kekyo/ExtremeFeedbackDevice/images/v1/AssembleFinishing.jpg

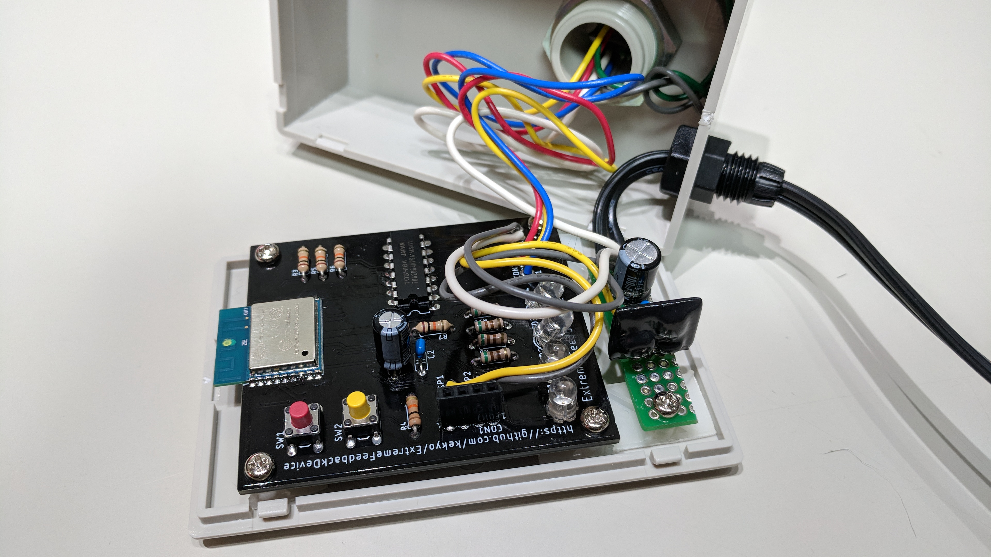
images/v1/AssembleFinishing.jpg
