kekyo/ExtremeFeedbackDevice/images/v1/AssembleUnit1.jpg

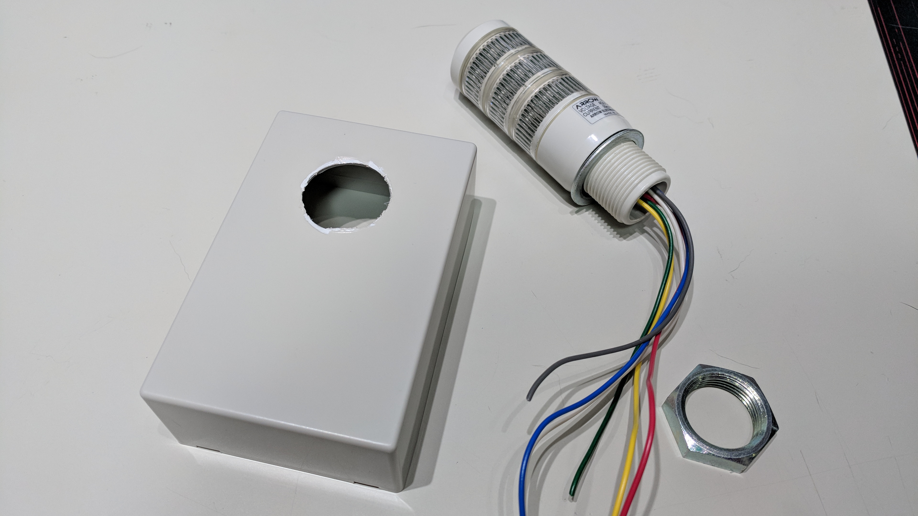
images/v1/AssembleUnit1.jpg
