kekyo/ExtremeFeedbackDevice/images/v1/AssembleUnit2.jpg

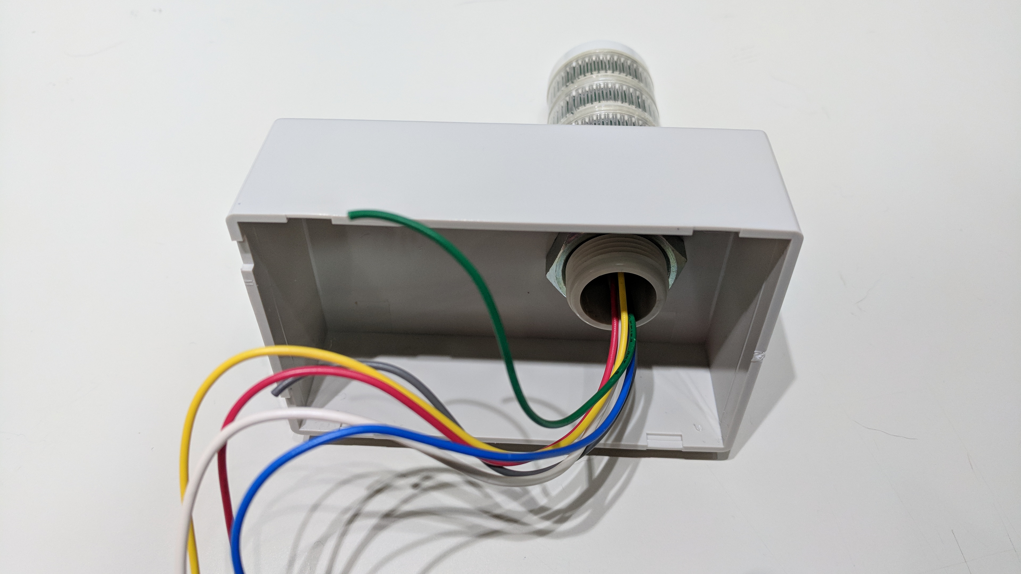
images/v1/AssembleUnit2.jpg
