kekyo/ExtremeFeedbackDevice/images/v1/AssembleUnit4.jpg

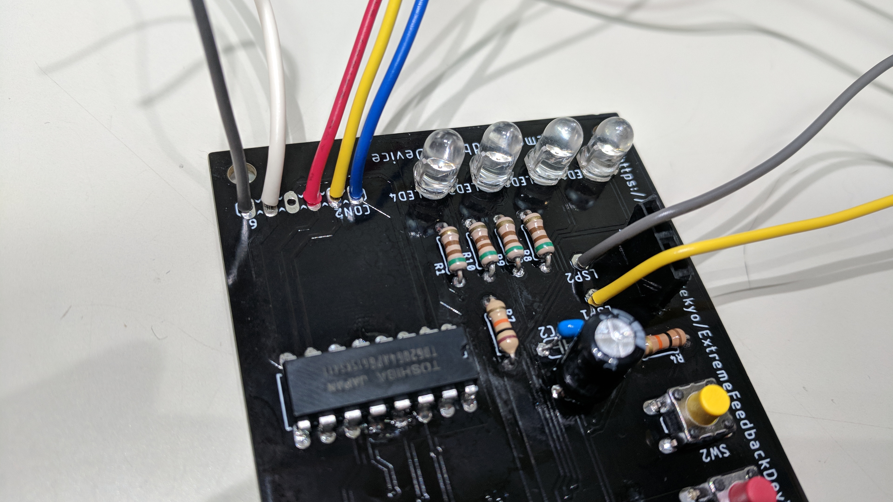
images/v1/AssembleUnit4.jpg
