kekyo/ExtremeFeedbackDevice/images/v1/Soldered2.jpg

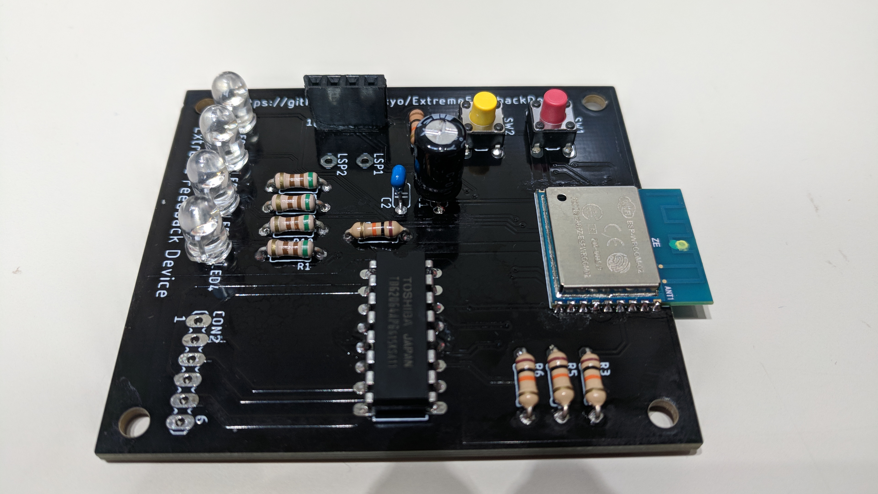
images/v1/Soldered2.jpg
